wenkeli/impedance_meter/firmware/UTFT/DefaultFonts.c

// DO NOT ADD YOUR OWN FONTS TO THIS FILE
// If you want to use your own fonts you should just drop the font .c file into your sketch folder.
// ------------------------------------------------------------------------------------------------

#define PROGMEM
#define fontdatatype const unsigned char

// SmallFont.c 
// Font Size	: 8x12
// Memory usage	: 1144 bytes
// # characters	: 95

fontdatatype SmallFont[1144] PROGMEM={         
0x08,0x0C,0x20,0x5F,
0x00,0x00,0x00,0x00,0x00,0x00,0x00,0x00,0x00,0x00,0x00,0x00, // <Space>
0x00,0x00,0x20,0x20,0x20,0x20,0x20,0x20,0x00,0x20,0x00,0x00, // !
0x00,0x28,0x50,0x50,0x00,0x00,0x00,0x00,0x00,0x00,0x00,0x00, // "
0x00,0x00,0x28,0x28,0xFC,0x28,0x50,0xFC,0x50,0x50,0x00,0x00, // #
0x00,0x20,0x78,0xA8,0xA0,0x60,0x30,0x28,0xA8,0xF0,0x20,0x00, // $
0x00,0x00,0x48,0xA8,0xB0,0x50,0x28,0x34,0x54,0x48,0x00,0x00, // %
0x00,0x00,0x20,0x50,0x50,0x78,0xA8,0xA8,0x90,0x6C,0x00,0x00, // &
0x00,0x40,0x40,0x80,0x00,0x00,0x00,0x00,0x00,0x00,0x00,0x00, // '
0x00,0x04,0x08,0x10,0x10,0x10,0x10,0x10,0x10,0x08,0x04,0x00, // (
0x00,0x40,0x20,0x10,0x10,0x10,0x10,0x10,0x10,0x20,0x40,0x00, // )
0x00,0x00,0x00,0x20,0xA8,0x70,0x70,0xA8,0x20,0x00,0x00,0x00, // *
0x00,0x00,0x20,0x20,0x20,0xF8,0x20,0x20,0x20,0x00,0x00,0x00, // +
0x00,0x00,0x00,0x00,0x00,0x00,0x00,0x00,0x00,0x40,0x40,0x80, // ,
0x00,0x00,0x00,0x00,0x00,0xF8,0x00,0x00,0x00,0x00,0x00,0x00, // -
0x00,0x00,0x00,0x00,0x00,0x00,0x00,0x00,0x00,0x40,0x00,0x00, // .
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
};
