wenkeli/impedance_meter/firmware/libmaple/wirish/boards/HY_MiniSTM32V/board.cpp

#include <board/board.h>         // For this board's header file

#include <wirish/wirish_types.h> // For stm32_pin_info and its contents
                                 // (these go into PIN_MAP).

#include <libmaple/fsmc.h>
#include <libmaple/gpio.h>
#include <libmaple/rcc.h>
#include <libmaple/timer.h>

void boardInit(void) {
	__io uint32 *mapr = &AFIO_BASE->MAPR;
	*mapr = ((*mapr) & ~(7 << 24) & AFIO_MAPR_SPI1_REMAP )
		| AFIO_MAPR_TIM1_REMAP | AFIO_MAPR_TIM4_REMAP
		| AFIO_MAPR_TIM3_REMAP_FULL //| BIT(8) | BIT(11)
		| AFIO_MAPR_USART2_REMAP | AFIO_MAPR_USART3_REMAP
		| AFIO_MAPR_SWJ_CFG_NO_JTAG_SW;
}

extern const stm32_pin_info PIN_MAP[BOARD_NR_GPIO_PINS] = {
    {GPIOA, TIMER5, ADC1,  0, 1,    0}, /* D00/PA0  */
    {GPIOA, TIMER5, ADC1,  1, 2,    1}, /* D01/PA1  */
    {GPIOA, TIMER5, ADC1,  2, 3,    2}, /* D02/PA2  */
    {GPIOA, TIMER5, ADC1,  3, 4,    3}, /* D03/PA3  */
    {GPIOA,   NULL, ADC1,  4, 0,    4}, /* D04/PA4  */
    {GPIOA,   NULL, ADC1,  5, 0,    5}, /* D05/PA5  */
    {GPIOA,   NULL, ADC1,  6, 0,    6}, /* D06/PA6  */ // ala check TIMER3
    {GPIOA,   NULL, ADC1,  7, 0,    7}, /* D07/PA7  */
    {GPIOA,   NULL, NULL,  8, 0, ADCx}, /* D08/PA8  */ // remap out
    {GPIOA,   NULL, NULL,  9, 0, ADCx}, /* D09/PA9  */ // remap out
    {GPIOA,   NULL, NULL, 10, 0, ADCx}, /* D10/PA10 */ // remap out
    {GPIOA,   NULL, NULL, 11, 0, ADCx}, /* D11/PA11 */ // remap out
    {GPIOA,   NULL, NULL, 12, 0, ADCx}, /* D12/PA12 */
    {GPIOA,   NULL, NULL, 13, 0, ADCx}, /* D13/PA13 */
    {GPIOA,   NULL, NULL, 14, 0, ADCx}, /* D14/PA14 */
    {GPIOA,	  NULL, NULL, 15, 0, ADCx}, /* D15/PA15 */ // remap in

    {GPIOB,   NULL, ADC1,  0, 0,    8}, /* D16/PB0  */
    {GPIOB,   NULL, ADC1,  1, 0,    9}, /* D17/PB1  */
    {GPIOB,   NULL, NULL,  2, 0, ADCx}, /* D18/PB2  */
    {GPIOB,   NULL, NULL,  3, 0, ADCx}, /* D19/PB3  */ // remap in
    {GPIOB,   NULL, NULL,  4, 0, ADCx}, /* D20/PB4  */ // remap in
    {GPIOB,   NULL, NULL,  5, 0, ADCx}, /* D21/PB5  */ // remap in
    {GPIOB,   NULL, NULL,  6, 0, ADCx}, /* D22/PB6  */ // remap out
    {GPIOB,   NULL, NULL,  7, 0, ADCx}, /* D23/PB7  */ // remap out
    {GPIOB,   NULL, NULL,  8, 0, ADCx}, /* D24/PB8  */ // remap out
    {GPIOB,   NULL, NULL,  9, 0, ADCx}, /* D25/PB9  */ // remap out
    {GPIOB,   NULL, NULL, 10, 0, ADCx}, /* D26/PB10 */
    {GPIOB,   NULL, NULL, 11, 0, ADCx}, /* D27/PB11 */
    {GPIOB,   NULL, NULL, 12, 0, ADCx}, /* D28/PB12 */
    {GPIOB,   NULL, NULL, 13, 0, ADCx}, /* D29/PB13 */
    {GPIOB,   NULL, NULL, 14, 0, ADCx}, /* D30/PB14 */
    {GPIOB,   NULL, NULL, 15, 0, ADCx}, /* D31/PB15 */

    {GPIOC,   NULL, ADC1,  0, 0,   10}, /* D32/PC0  */
    {GPIOC,   NULL, ADC1,  1, 0,   11}, /* D33/PC1  */
    {GPIOC,   NULL, ADC1,  2, 0,   12}, /* D34/PC2  */
    {GPIOC,   NULL, ADC1,  3, 0,   13}, /* D35/PC3  */
    {GPIOC,   NULL, ADC1,  4, 0,   14}, /* D36/PC4  */
    {GPIOC,   NULL, ADC1,  5, 0,   15}, /* D37/PC5  */
    {GPIOC, TIMER3, NULL,  6, 1, ADCx}, /* D38/PC6  */
    {GPIOC, TIMER3, NULL,  7, 2, ADCx}, /* D39/PC7  */
    {GPIOC, TIMER3, NULL,  8, 3, ADCx}, /* D40/PC8  */
    {GPIOC, TIMER3, NULL,  9, 4, ADCx}, /* D41/PC9  */
    {GPIOC,   NULL, NULL, 10, 0, ADCx}, /* D42/PC10 */
    {GPIOC,   NULL, NULL, 11, 0, ADCx}, /* D43/PC11 */
    {GPIOC,   NULL, NULL, 12, 0, ADCx}, /* D44/PC12 */
    {GPIOC,   NULL, NULL, 13, 0, ADCx}, /* D45/PC13 */
    {GPIOC,   NULL, NULL, 14, 0, ADCx}, /* D46/PC14 */
    {GPIOC,   NULL, NULL, 15, 0, ADCx}, /* D47/PC15 */

    {GPIOD,   NULL, NULL,  0, 0, ADCx}, /* D48/PD0  */
    {GPIOD,   NULL, NULL,  1, 0, ADCx}, /* D49/PD1  */
    {GPIOD,   NULL, NULL,  2, 0, ADCx}, /* D50/PD2  */
    {GPIOD,   NULL, NULL,  3, 0, ADCx}, /* D51/PD3  */
    {GPIOD,   NULL, NULL,  4, 0, ADCx}, /* D52/PD4  */
    {GPIOD,   NULL, NULL,  5, 0, ADCx}, /* D53/PD5  */
    {GPIOD,   NULL, NULL,  6, 0, ADCx}, /* D54/PD6  */
    {GPIOD,   NULL, NULL,  7, 0, ADCx}, /* D55/PD7  */
    {GPIOD,   NULL, NULL,  8, 0, ADCx}, /* D56/PD8  */
    {GPIOD,   NULL, NULL,  9, 0, ADCx}, /* D57/PD9  */
    {GPIOD,   NULL, NULL, 10, 0, ADCx}, /* D58/PD10 */
    {GPIOD,   NULL, NULL, 11, 0, ADCx}, /* D59/PD11 */
    {GPIOD, TIMER4, NULL, 12, 1, ADCx}, /* D60/PD12 */  // remap in
    {GPIOD, TIMER4, NULL, 13, 2, ADCx}, /* D61/PD13 */  // remap in
    {GPIOD, TIMER4, NULL, 14, 3, ADCx}, /* D62/PD14 */  // remap in
    {GPIOD, TIMER4, NULL, 15, 4, ADCx}, /* D63/PD15 */  // remap in

    {GPIOE,   NULL, NULL,  0, 0, ADCx}, /* D64/PE0  */
    {GPIOE,   NULL, NULL,  1, 0, ADCx}, /* D65/PE1  */
    {GPIOE,   NULL, NULL,  2, 0, ADCx}, /* D66/PE2  */
    {GPIOE,   NULL, NULL,  3, 0, ADCx}, /* D67/PE3  */
    {GPIOE,   NULL, NULL,  4, 0, ADCx}, /* D68/PE4  */
    {GPIOE,   NULL, NULL,  5, 0, ADCx}, /* D69/PE5  */
    {GPIOE,   NULL, NULL,  6, 0, ADCx}, /* D70/PE6  */
    {GPIOE,   NULL, NULL,  7, 0, ADCx}, /* D71/PE7  */
    {GPIOE,   NULL, NULL,  8, 0, ADCx}, /* D72/PE8  */
    {GPIOE, TIMER1, NULL,  9, 1, ADCx}, /* D73/PE9  */  // remap in
    {GPIOE,   NULL, NULL, 10, 0, ADCx}, /* D74/PE10 */
    {GPIOE, TIMER1, NULL, 11, 2, ADCx}, /* D75/PE11 */  // remap in
    {GPIOE,   NULL, NULL, 12, 0, ADCx}, /* D76/PE12 */
    {GPIOE, TIMER1, NULL, 13, 3, ADCx}, /* D77/PE13 */  // remap in
    {GPIOE, TIMER1, NULL, 14, 4, ADCx}, /* D78/PE14 */  // remap in
    {GPIOE,   NULL, NULL, 15, 0, ADCx}  /* D79/PE15 */
};

extern const uint8 boardPWMPins[BOARD_NR_PWM_PINS] __FLASH__ = {
    0, 1, 2, 3, 38, 39, 49, 41, 60, 61, 62, 63, 73, 75, 77, 78
};

extern const uint8 boardADCPins[BOARD_NR_ADC_PINS] __FLASH__ = {
    0, 1, 2, 3, 4, 5, 6, 7, 16, 17, 32, 33, 34, 35, 36, 37
};

extern const uint8 boardUsedPins[BOARD_NR_USED_PINS] __FLASH__ = {
    BOARD_LED_PIN, BOARD_LED1_PIN, BOARD_BUTTON_PIN, BOARD_BUTTON1_PIN,
    BOARD_JTMS_SWDIO_PIN, BOARD_JTCK_SWCLK_PIN, BOARD_JTDI_PIN,
    BOARD_JTDO_PIN, BOARD_NJTRST_PIN, Port2Pin('A', 4), Port2Pin('A', 5),
    Port2Pin('A', 6), Port2Pin('A', 7), Port2Pin('A', 11), Port2Pin('A', 12),
    Port2Pin('D', 0), Port2Pin('D', 1), Port2Pin('D', 4), Port2Pin('D', 5),
    Port2Pin('D', 7), Port2Pin('D', 8), Port2Pin('D', 9), Port2Pin('D', 10),
    Port2Pin('D', 11), Port2Pin('D', 14), Port2Pin('D', 15), Port2Pin('E', 7),
    Port2Pin('E', 8), Port2Pin('E', 9), Port2Pin('E', 10), Port2Pin('E', 11),
    Port2Pin('E', 12), Port2Pin('E', 13), Port2Pin('E', 14), Port2Pin('E', 15)
};
